mikaelsundin/dcc_block_detector/code/inc/array_fn.h

#ifndef _ARRAY_FN_H_
#define _ARRAY_FN_H_

#include <stdint.h>

uint16_t get_array16_min(uint16_t *bfr, uint8_t offset, uint8_t count);
uint16_t get_array16_max(uint16_t *bfr, uint8_t offset, uint8_t count);


#endif
